Dovgalyuk/SoundDecoderLib/decodervm/vm.c

#include <stdio.h>
#include <stdlib.h>
#include <inttypes.h>
#include "vm.h"
#include "slot.h"
#include "schedule.h"
#include "audio.h"
#include "utils.h"
#include "cv.h"
#include "engine.h"
#include "logger.h"

#define INSTRUCTIONS_PER_TICK 100

static Slot slots[VM_SLOTS];
static uint8_t memory[VAR_GLOBAL_SIZE];
static bool trigger_set;

void vm_set_var(uint16_t addr, uint8_t val)
{
    addr -= VAR_GLOBAL_START;
    if (addr < VAR_GLOBAL_SIZE) {
        memory[addr] = val;
    }
}

uint8_t vm_get_var(uint16_t addr)
{
    addr -= VAR_GLOBAL_START;
    if (addr >= VAR_GLOBAL_SIZE) {
        return 0;
    }
    return memory[addr];
}

bool vm_load_slot(FILE *f)
{
    uint8_t slot;
    char *name = NULL;
    Schedule *sch = NULL;
    if (!file_read_uint8(f, &slot)) {
        printf("error %d\n", __LINE__);
        goto error;
    }
    if (slot >= VM_SLOTS || slots[slot].schedule) {
        printf("error %d\n", __LINE__);
        goto error;
    }
    if (!file_read_string(f, &name)) {
        printf("error %d\n", __LINE__);
        goto error;
    }
    uint8_t volume, flags;
    if (!file_read_uint8(f, &volume)) {
        printf("error %d\n", __LINE__);
        goto error;
    }
    if (!file_read_uint8(f, &flags)) {
        printf("error %d\n", __LINE__);
        goto error;
    }
    uint32_t init, length;
    if (!file_read_uint32(f, &init)) {
        printf("error %d\n", __LINE__);
        goto error;
    }
    if (!file_read_uint32(f, &length)) {
        printf("error %d\n", __LINE__);
        goto error;
    }
    sch = malloc(sizeof(Schedule) + length);
    if (!sch) {
        printf("Not enough memory while loading slot %d of size %"PRId32"\n", slot, length);
        goto error;
    }
    sch->name = name;
    sch->volume = volume;
    sch->flags = flags;
    sch->start = init;
    sch->script_size = length;
    if (fread(sch->script, 1, length, f) != length) {
        printf("error %d\n", __LINE__);
        goto error;
    }
    //printf("Loading slot %d (%s) with %d bytes\n", slot, sch->name, sch->script_size);
    slots[slot].id = slot;
    slot_init(&slots[slot], sch);
    return true;
error:
    free(name);
    free(sch);
    return false;
}

void vm_set_slot_var(uint8_t id, uint16_t addr, uint8_t val)
{
    if (id < VM_SLOTS) {
        slot_set_var(&slots[id], addr, val);
    }
}

uint8_t vm_get_slot_var(uint8_t id, uint16_t addr)
{
    if (id >= VM_SLOTS) {
        return 0;
    }
    return slot_get_var(&slots[id], addr);
}

bool vm_slot_is_brake(uint8_t id)
{
    return id < VM_SLOTS && slots[id].schedule
        && (slots[id].schedule->flags & SCHEDULE_FLAG_BRAKE);
}

void vm_tick(uint32_t t)
{
    static int32_t trigger_time;
    /* Set trigger */
    //trigger_time += t;
    // project mogul
    // uint32_t period = 950 - vm_get_var(V_SPEED) * 3;
    // project mogul2
    int32_t period = cv_read(CV_CHUFF_PERIOD) * 10
                     - (int32_t)vm_get_var(V_SPEED) * cv_read(CV_CHUFF_SPEEDUP) / 2;
    int32_t min = cv_read(CV_CHUFF_MIN_PERIOD);
    if (period < min) {
        /* For highest speed need not to be prototypical */
        period = min;
    }
    trigger_time += t;
    if (trigger_time >= period) {
        trigger_time -= period;
        if (engine_get_speed_step()) {
            trigger_set = true;
        }
    }

    static uint32_t clock_time, clock_time_256;
    clock_time += t;
    clock_time_256 += t;
    while (clock_time >= 1000) {
        clock_time -= 1000;
        /* Decrement timers */
        for (int i = 0 ; i < VM_SLOTS ; ++i) {
            if (!slots[i].schedule) {
                continue;
            }
            uint8_t v = slot_get_var(&slots[i], V_TIMER_1S);
            if (v) {
                slot_set_var(&slots[i], V_TIMER_1S, v - 1);
            }
        }
    }
    while (clock_time_256 >= 256) {
        clock_time_256 -= 256;
        /* Decrement timers */
        for (int i = 0 ; i < VM_SLOTS ; ++i) {
            if (!slots[i].schedule) {
                continue;
            }
            uint8_t v = slot_get_var(&slots[i], V_TIMER_1_256MS);
            if (v) {
                slot_set_var(&slots[i], V_TIMER_1_256MS, v - 1);
            }
            v = slot_get_var(&slots[i], V_TIMER_2_256MS);
            if (v) {
                slot_set_var(&slots[i], V_TIMER_2_256MS, v - 1);
            }
        }
    }
    /* Run instructions */
    for (int j = 0 ; j < INSTRUCTIONS_PER_TICK ; ++j) {
        // trigger_time += 1;
        // if (trigger_time >= period) {
        //     trigger_time -= period;
        //     trigger_set = true;
        // }
        /* Trigger at any speed to allow correct emergency stop */
        vm_set_var(F_TRIGGER, trigger_set);

        for (int i = 0 ; i < VM_SLOTS ; ++i) {
            /* TODO?: brake function */
            if (slots[i].schedule
                && (slots[i].schedule->flags & SCHEDULE_FLAG_BRAKE)
                && (vm_get_var(F_DISABLE_BRAKE)
                    /* Brake script may not check function */
                    || !slot_get_var(&slots[i], F_FUNCTION))) {
                continue;
            }

            slot_step(&slots[i]);
        }
    }
}

void vm_reset_trigger(void)
{
    trigger_set = false;
}

bool vm_has_drivelock(void)
{
    for (int i = 0 ; i < VM_SLOTS ; ++i) {
        if (!slots[i].schedule) {
            continue;
        }
        if (slot_get_var(&slots[i], F_DRIVELOCK)) {
            return true;
        }
    }
    return false;
}

void vm_clear(void)
{
    for (int i = 0 ; i < VM_SLOTS ; ++i) {
        slot_clear(&slots[i]);
    }
}

void vm_reset(void)
{
    trigger_set = false;
    vm_init_function_keys();
    for (int i = 0 ; i < VM_SLOTS ; ++i) {
        slot_reset(&slots[i]);
    }
}

void vm_set_function_key(uint8_t f, bool v)
{
    if (f < VM_FUNCTION_KEYS) {
        vm_set_var(F_KEY0 + f, v);
    }
}

bool vm_get_function_key(uint8_t f)
{
    if (f < VM_FUNCTION_KEYS) {
        return vm_get_var(F_KEY0 + f);
    }
    return false;
}

void vm_init_function_keys(void)
{
    for (int i = 0 ; i < 4 ; ++i) {
        uint8_t bits = cv_read(CV_FUNC_DEFAULT0 + i);
        for (int j = 0 ; j < 8 ; ++j, bits >>= 1) {
            vm_set_function_key(i * 8 + j, bits & 1);
        }
    }
}
